machdyne/einszeit/fw/test/host/ezlib/sp80022.py

"""NIST SP 800-22 Rev 1a statistical test suite.

These tests answer "does this look random", which is a much weaker question
than "how much entropy does this carry". A well-seeded DRBG passes all fifteen
and is still useless as one-time-pad material. They are included because the
RP2350 TRNG documentation claims FIPS 140-2 conformance and because a failure
here is a strong signal that something is wrong with the capture path.

Each test returns one or more p-values. A p-value below 0.01 fails at the
conventional significance level.
"""

from __future__ import annotations

import math
from dataclasses import dataclass, field

import numpy as np
from scipy.special import erfc, gammaincc

ALPHA = 0.01


@dataclass
class TestResult:
    name: str
    p_values: list
    passed: bool
    detail: dict = field(default_factory=dict)
    skipped: str = ""

    @property
    def p_value(self) -> float:
        return self.p_values[0] if self.p_values else float("nan")


def _res(name, p, detail=None, skipped=""):
    ps = [p] if isinstance(p, float) else list(p)
    ok = all(v >= ALPHA for v in ps if v == v) if ps else False
    return TestResult(name, ps, ok, detail or {}, skipped)


def _skip(name, why):
    return TestResult(name, [], True, {}, skipped=why)


# --------------------------------------------------------------------------

def frequency(bits: np.ndarray) -> TestResult:
    n = bits.size
    s = int(bits.sum()) * 2 - n
    s_obs = abs(s) / math.sqrt(n)
    return _res("Frequency (monobit)", float(erfc(s_obs / math.sqrt(2))),
                {"sum": s, "s_obs": s_obs})


def block_frequency(bits: np.ndarray, m: int = 128) -> TestResult:
    n = bits.size
    nblocks = n // m
    if nblocks < 1:
        return _skip("Block frequency", "not enough bits")
    pi = bits[: nblocks * m].reshape(nblocks, m).mean(axis=1)
    chi2 = 4.0 * m * float(((pi - 0.5) ** 2).sum())
    return _res("Block frequency", float(gammaincc(nblocks / 2.0, chi2 / 2.0)),
                {"M": m, "N": nblocks, "chi2": chi2})


def runs(bits: np.ndarray) -> TestResult:
    n = bits.size
    pi = float(bits.mean())
    if abs(pi - 0.5) >= 2.0 / math.sqrt(n):
        return _res("Runs", 0.0, {"pi": pi, "note": "failed the monobit pre-test"})
    v = int((bits[1:] != bits[:-1]).sum()) + 1
    num = abs(v - 2.0 * n * pi * (1 - pi))
    den = 2.0 * math.sqrt(2.0 * n) * pi * (1 - pi)
    return _res("Runs", float(erfc(num / den)), {"pi": pi, "V": v})


_LONGRUN = {
    128: (8, 3, 49, [0.2148, 0.3672, 0.2305, 0.1875], 4),
    512: (16, 4, 49, [0.1174, 0.2430, 0.2493, 0.1752, 0.1027, 0.1124], 6),
    10000: (24, 6, 75, [0.0882, 0.2092, 0.2483, 0.1933, 0.1208, 0.0675, 0.0727], 10),
}


def longest_run(bits: np.ndarray) -> TestResult:
    n = bits.size
    if n >= 750_000:
        m = 10000
    elif n >= 6272:
        m = 128
    else:
        return _skip("Longest run of ones", "needs at least 6272 bits")

    _, k, n_blocks, probs, vmin = _LONGRUN[m]
    avail = n // m
    if avail < n_blocks:
        n_blocks = avail
    if n_blocks < 1:
        return _skip("Longest run of ones", "not enough blocks")

    counts = np.zeros(k + 1, dtype=np.int64)
    for i in range(n_blocks):
        block = bits[i * m : (i + 1) * m]
        longest = best = 0
        for b in block:
            best = best + 1 if b else 0
            if best > longest:
                longest = best
        idx = min(max(longest - vmin, 0), k)
        counts[idx] += 1

    exp = np.array(probs) * n_blocks
    chi2 = float((((counts - exp) ** 2) / exp).sum())
    return _res("Longest run of ones", float(gammaincc(k / 2.0, chi2 / 2.0)),
                {"M": m, "N": n_blocks, "chi2": chi2, "counts": counts.tolist()})


def binary_matrix_rank(bits: np.ndarray, m: int = 32, q: int = 32) -> TestResult:
    n = bits.size
    nmat = n // (m * q)
    if nmat < 38:
        return _skip("Binary matrix rank", "needs at least 38 matrices (38912 bits)")

    data = bits[: nmat * m * q].reshape(nmat, m, q).astype(np.uint8)
    ranks = np.array([_gf2_rank(mat) for mat in data])
    f_full = int((ranks == m).sum())
    f_one = int((ranks == m - 1).sum())
    f_rest = nmat - f_full - f_one

    probs = np.array([0.2888, 0.5776, 0.1336])
    obs = np.array([f_full, f_one, f_rest], dtype=np.float64)
    exp = probs * nmat
    chi2 = float((((obs - exp) ** 2) / exp).sum())
    return _res("Binary matrix rank", float(math.exp(-chi2 / 2.0)),
                {"matrices": nmat, "full": f_full, "full_minus_1": f_one,
                 "lower": f_rest, "chi2": chi2})


def _gf2_rank(mat: np.ndarray) -> int:
    m = mat.copy().astype(np.uint8)
    rows, cols = m.shape
    rank = 0
    for col in range(cols):
        pivot = None
        for r in range(rank, rows):
            if m[r, col]:
                pivot = r
                break
        if pivot is None:
            continue
        if pivot != rank:
            m[[rank, pivot]] = m[[pivot, rank]]
        sel = m[rank + 1 :, col] == 1
        if sel.any():
            m[rank + 1 :][sel] ^= m[rank]
        rank += 1
        if rank == rows:
            break
    return rank


def spectral_dft(bits: np.ndarray) -> TestResult:
    n = bits.size
    if n < 1000:
        return _skip("DFT (spectral)", "needs at least 1000 bits")
    x = bits.astype(np.float64) * 2.0 - 1.0
    mags = np.abs(np.fft.rfft(x)[: n // 2])
    threshold = math.sqrt(math.log(1.0 / 0.05) * n)
    n0 = 0.95 * n / 2.0
    n1 = float((mags < threshold).sum())
    d = (n1 - n0) / math.sqrt(n * 0.95 * 0.05 / 4.0)
    return _res("DFT (spectral)", float(erfc(abs(d) / math.sqrt(2))),
                {"threshold": threshold, "peaks_below": n1, "expected": n0})


_TEMPLATES_9 = [
    "000000001", "000000011", "000000101", "000001011", "000010011",
    "000100011", "000101001", "001001011", "001010011", "010101011",
]


def non_overlapping_template(bits: np.ndarray, m: int = 9,
                             nblocks: int = 8) -> TestResult:
    n = bits.size
    block_len = n // nblocks
    if block_len < m + 1:
        return _skip("Non-overlapping template", "not enough bits")

    packed = np.packbits(bits)
    del packed
    mu = (block_len - m + 1) / (2.0 ** m)
    var = block_len * (1.0 / 2.0 ** m - (2.0 * m - 1.0) / 2.0 ** (2 * m))
    if var <= 0:
        return _skip("Non-overlapping template", "variance underflow")

    p_values = []
    for tpl in _TEMPLATES_9:
        t = np.frombuffer(tpl.encode(), dtype=np.uint8) - ord("0")
        w = np.empty(nblocks)
        for j in range(nblocks):
            block = bits[j * block_len : (j + 1) * block_len]
            w[j] = _count_non_overlapping(block, t)
        chi2 = float((((w - mu) ** 2) / var).sum())
        p_values.append(float(gammaincc(nblocks / 2.0, chi2 / 2.0)))

    npass = sum(1 for p in p_values if p >= ALPHA)
    return TestResult(
        "Non-overlapping template", p_values,
        npass == len(p_values),
        {"m": m, "templates": len(_TEMPLATES_9), "passed": npass,
         "min_p": min(p_values)},
    )


def _count_non_overlapping(block: np.ndarray, tpl: np.ndarray) -> int:
    m = tpl.size
    if block.size < m:
        return 0
    view = np.lib.stride_tricks.sliding_window_view(block, m)
    hits = np.flatnonzero((view == tpl).all(axis=1))
    count = 0
    last = -m
    for h in hits:
        if h >= last + m:
            count += 1
            last = h
    return count


def overlapping_template(bits: np.ndarray, m: int = 9) -> TestResult:
    n = bits.size
    block_len = 1032
    nblocks = n // block_len
    if nblocks < 10:
        return _skip("Overlapping template", "needs at least 10320 bits")

    tpl = np.ones(m, dtype=np.uint8)
    probs = [0.364091, 0.185659, 0.139381, 0.100571, 0.070432, 0.139865]
    counts = np.zeros(6, dtype=np.int64)

    for j in range(nblocks):
        block = bits[j * block_len : (j + 1) * block_len]
        view = np.lib.stride_tricks.sliding_window_view(block, m)
        hits = int((view == tpl).all(axis=1).sum())
        counts[min(hits, 5)] += 1

    exp = np.array(probs) * nblocks
    chi2 = float((((counts - exp) ** 2) / exp).sum())
    return _res("Overlapping template", float(gammaincc(5 / 2.0, chi2 / 2.0)),
                {"N": nblocks, "chi2": chi2, "counts": counts.tolist()})


_MAURER = {
    6: (640, 5.2177052, 2.954), 7: (1280, 6.1962507, 3.125),
    8: (2560, 7.1836656, 3.238), 9: (5120, 8.1764248, 3.311),
    10: (10240, 9.1723243, 3.356), 11: (20480, 10.170032, 3.384),
    12: (40960, 11.168765, 3.401), 13: (81920, 12.168070, 3.410),
    14: (163840, 13.167693, 3.416), 15: (327680, 14.167488, 3.419),
    16: (655360, 15.167379, 3.421),
}


def maurer_universal(bits: np.ndarray) -> TestResult:
    n = bits.size
    chosen = None
    for L in range(16, 5, -1):
        q, _, _ = _MAURER[L][0], 0, 0
        if n >= (_MAURER[L][0] + 1000) * L:
            chosen = L
            break
    if chosen is None:
        return _skip("Maurer universal", "needs at least 387840 bits")

    L = chosen
    q, expected, variance = _MAURER[L]
    nblocks = n // L
    k = nblocks - q
    if k <= 0:
        return _skip("Maurer universal", "not enough blocks")

    blocks = bits[: nblocks * L].reshape(nblocks, L)
    weights = (1 << np.arange(L - 1, -1, -1)).astype(np.int64)
    vals = blocks.astype(np.int64) @ weights

    table = np.zeros(1 << L, dtype=np.int64)
    for i in range(q):
        table[vals[i]] = i + 1

    total = 0.0
    for i in range(q, nblocks):
        v = vals[i]
        total += math.log2(i + 1 - table[v]) if table[v] else math.log2(i + 1)
        table[v] = i + 1

    fn = total / k
    c = 0.7 - 0.8 / L + (4 + 32.0 / L) * (k ** (-3.0 / L)) / 15.0
    sigma = c * math.sqrt(variance / k)
    p = float(erfc(abs((fn - expected) / (math.sqrt(2) * sigma))))
    return _res("Maurer universal", p,
                {"L": L, "Q": q, "K": k, "fn": fn, "expected": expected})


def _berlekamp_massey(bits_int: int, n: int) -> int:
    """Linear complexity over GF(2), polynomials held as Python integers."""
    c, b = 1, 1
    ll, m = 0, -1
    for i in range(n):
        d = (bits_int >> (n - 1 - i)) & 1
        for j in range(1, ll + 1):
            if (c >> j) & 1:
                d ^= (bits_int >> (n - 1 - (i - j))) & 1
        if d:
            t = c
            c ^= b << (i - m)
            if 2 * ll <= i:
                ll = i + 1 - ll
                m = i
                b = t
    return ll


def linear_complexity(bits: np.ndarray, m: int = 500) -> TestResult:
    n = bits.size
    nblocks = n // m
    if nblocks < 200:
        return _skip("Linear complexity", "needs at least 100000 bits")
    nblocks = min(nblocks, 1000)  # keeps the run time sane

    mu = m / 2.0 + (9.0 + (-1) ** (m + 1)) / 36.0 - (m / 3.0 + 2.0 / 9.0) / 2.0 ** m
    probs = [0.010417, 0.03125, 0.125, 0.5, 0.25, 0.0625, 0.020833]
    counts = np.zeros(7, dtype=np.int64)

    packed = np.packbits(bits[: nblocks * m])
    for j in range(nblocks):
        block = bits[j * m : (j + 1) * m]
        as_int = int.from_bytes(np.packbits(block).tobytes(), "big") >> (
            (-m) % 8
        )
        li = _berlekamp_massey(as_int, m)
        t = ((-1) ** m) * (li - mu) + 2.0 / 9.0
        if t <= -2.5:
            idx = 0
        elif t <= -1.5:
            idx = 1
        elif t <= -0.5:
            idx = 2
        elif t <= 0.5:
            idx = 3
        elif t <= 1.5:
            idx = 4
        elif t <= 2.5:
            idx = 5
        else:
            idx = 6
        counts[idx] += 1
    del packed

    exp = np.array(probs) * nblocks
    chi2 = float((((counts - exp) ** 2) / exp).sum())
    return _res("Linear complexity", float(gammaincc(6 / 2.0, chi2 / 2.0)),
                {"M": m, "N": nblocks, "chi2": chi2, "counts": counts.tolist()})


def _psi2(bits: np.ndarray, m: int) -> float:
    if m <= 0:
        return 0.0
    n = bits.size
    ext = np.concatenate([bits, bits[: m - 1]]) if m > 1 else bits
    ids = np.zeros(n, dtype=np.int64)
    for j in range(m):
        ids = ids * 2 + ext[j : j + n]
    counts = np.bincount(ids, minlength=1 << m).astype(np.float64)
    return float((counts ** 2).sum() * (2 ** m) / n - n)


def serial(bits: np.ndarray, m: int = 16) -> TestResult:
    n = bits.size
    while m > 2 and m >= math.floor(math.log2(n)) - 2:
        m -= 1
    if m < 2:
        return _skip("Serial", "not enough bits")

    p1 = _psi2(bits, m)
    p2 = _psi2(bits, m - 1)
    p3 = _psi2(bits, m - 2)
    d1 = p1 - p2
    d2 = p1 - 2 * p2 + p3
    pa = float(gammaincc(2 ** (m - 2), d1 / 2.0))
    pb = float(gammaincc(2 ** (m - 3), d2 / 2.0))
    return _res("Serial", [pa, pb], {"m": m, "del1": d1, "del2": d2})


def approximate_entropy(bits: np.ndarray, m: int = 10) -> TestResult:
    n = bits.size
    while m > 2 and m > math.floor(math.log2(n)) - 5:
        m -= 1
    if m < 2:
        return _skip("Approximate entropy", "not enough bits")

    def phi(mm: int) -> float:
        ext = np.concatenate([bits, bits[:mm]])
        ids = np.zeros(n, dtype=np.int64)
        for j in range(mm):
            ids = ids * 2 + ext[j : j + n]
        counts = np.bincount(ids, minlength=1 << mm).astype(np.float64) / n
        nz = counts[counts > 0]
        return float((nz * np.log(nz)).sum())

    apen = phi(m) - phi(m + 1)
    chi2 = 2.0 * n * (math.log(2) - apen)
    return _res("Approximate entropy",
                float(gammaincc(2 ** (m - 1), chi2 / 2.0)),
                {"m": m, "ApEn": apen, "chi2": chi2})


def cumulative_sums(bits: np.ndarray) -> TestResult:
    n = bits.size
    x = bits.astype(np.int64) * 2 - 1
    ps = []
    for rev in (False, True):
        s = np.cumsum(x[::-1] if rev else x)
        z = int(np.abs(s).max())
        if z == 0:
            ps.append(1.0)
            continue
        total = 0.0
        from scipy.stats import norm
        k0 = int((-n / z + 1) // 4)
        k1 = int((n / z - 1) // 4)
        for k in range(k0, k1 + 1):
            total += norm.cdf((4 * k + 1) * z / math.sqrt(n))
            total -= norm.cdf((4 * k - 1) * z / math.sqrt(n))
        k0 = int((-n / z - 3) // 4)
        for k in range(k0, k1 + 1):
            total -= norm.cdf((4 * k + 3) * z / math.sqrt(n))
            total += norm.cdf((4 * k + 1) * z / math.sqrt(n))
        ps.append(max(0.0, min(1.0, 1.0 - total)))
    return _res("Cumulative sums", ps, {"forward": ps[0], "reverse": ps[1]})


_EXC_PI = {
    1: [0.5000, 0.2500, 0.1250, 0.0625, 0.0312, 0.0312],
    2: [0.7500, 0.0625, 0.0469, 0.0352, 0.0264, 0.0791],
    3: [0.8333, 0.0278, 0.0231, 0.0193, 0.0161, 0.0804],
    4: [0.8750, 0.0156, 0.0137, 0.0120, 0.0105, 0.0733],
    5: [0.9000, 0.0100, 0.0090, 0.0081, 0.0073, 0.0656],
    6: [0.9167, 0.0069, 0.0064, 0.0058, 0.0053, 0.0588],
    7: [0.9286, 0.0051, 0.0047, 0.0044, 0.0041, 0.0531],
}


def random_excursions(bits: np.ndarray) -> TestResult:
    n = bits.size
    x = bits.astype(np.int64) * 2 - 1
    s = np.concatenate(([0], np.cumsum(x), [0]))
    zero_idx = np.flatnonzero(s == 0)
    cycles = len(zero_idx) - 1
    if cycles < 500:
        return _skip("Random excursions", f"only {cycles} cycles, needs 500")

    states = [-4, -3, -2, -1, 1, 2, 3, 4]
    p_values = []
    detail = {}
    for st in states:
        counts = np.zeros(6, dtype=np.int64)
        for c in range(cycles):
            seg = s[zero_idx[c] : zero_idx[c + 1]]
            counts[min(int((seg == st).sum()), 5)] += 1
        pi = _EXC_PI[abs(st)]
        exp = np.array(pi) * cycles
        chi2 = float((((counts - exp) ** 2) / exp).sum())
        p = float(gammaincc(5 / 2.0, chi2 / 2.0))
        p_values.append(p)
        detail[str(st)] = {"chi2": chi2, "p": p}

    npass = sum(1 for p in p_values if p >= ALPHA)
    return TestResult("Random excursions", p_values, npass == len(p_values),
                      {"cycles": cycles, "passed": npass,
                       "min_p": min(p_values), "states": detail})


def random_excursions_variant(bits: np.ndarray) -> TestResult:
    n = bits.size
    x = bits.astype(np.int64) * 2 - 1
    s = np.concatenate(([0], np.cumsum(x), [0]))
    cycles = int((s == 0).sum()) - 1
    if cycles < 500:
        return _skip("Random excursions variant", f"only {cycles} cycles, needs 500")

    p_values = []
    for st in list(range(-9, 0)) + list(range(1, 10)):
        xi = int((s == st).sum())
        denom = math.sqrt(2.0 * cycles * (4.0 * abs(st) - 2.0))
        p_values.append(float(erfc(abs(xi - cycles) / denom)))

    npass = sum(1 for p in p_values if p >= ALPHA)
    return TestResult("Random excursions variant", p_values,
                      npass == len(p_values),
                      {"cycles": cycles, "passed": npass, "min_p": min(p_values)})


ALL_TESTS = [
    frequency, block_frequency, runs, longest_run, binary_matrix_rank,
    spectral_dft, non_overlapping_template, overlapping_template,
    maurer_universal, linear_complexity, serial, approximate_entropy,
    cumulative_sums, random_excursions, random_excursions_variant,
]


def run_all(bits: np.ndarray, skip_slow: bool = False) -> list:
    slow = {linear_complexity, non_overlapping_template, random_excursions}
    out = []
    for fn in ALL_TESTS:
        if skip_slow and fn in slow:
            out.append(_skip(fn.__name__.replace("_", " ").title(), "skipped (fast mode)"))
            continue
        try:
            out.append(fn(bits))
        except Exception as exc:  # a failed test must not lose the whole report
            out.append(TestResult(fn.__name__, [], False, {"error": str(exc)}))
    return out


def summarise(results: list) -> dict:
    ran = [r for r in results if not r.skipped and r.p_values]
    failed = [r.name for r in ran if not r.passed]
    return {
        "total": len(results),
        "ran": len(ran),
        "skipped": len(results) - len(ran),
        "failed": failed,
        "pass": len(failed) == 0,
    }


# ---------------------------------------------------------------------------
# Multi-sequence assessment
# ---------------------------------------------------------------------------
#
# SP 800-22 is not designed around a single p-value from one long sequence. The
# suite partitions the data into m sequences, runs every test on each, and
# applies two acceptance criteria: the proportion of sequences passing must
# fall inside a confidence interval, and the p-values must be uniformly
# distributed over (0,1).
#
# This also resolves the random excursion problem. Those two tests apply only
# to sequences whose +-1 walk returns to zero at least 500 times, and whether
# any single sequence qualifies is close to a coin toss: the number of returns
# behaves like sqrt(n)*|N(0,1)|, so even at 10^8 bits a sequence fails to
# qualify about 4% of the time. Across m sequences enough of them qualify, and
# the suite scores only those, which is exactly what NIST intends.

def proportion_bounds(m: int, alpha: float = ALPHA) -> tuple:
    """NIST acceptance interval for the proportion of passing sequences."""
    p_hat = 1.0 - alpha
    margin = 3.0 * math.sqrt(p_hat * alpha / m)
    return (max(0.0, p_hat - margin), min(1.0, p_hat + margin))


def pvalue_uniformity(p_values: list) -> float:
    """Chi-square over 10 equal bins; NIST rejects below 0.0001."""
    if len(p_values) < 10:
        return float("nan")
    counts = np.histogram(np.asarray(p_values), bins=10, range=(0.0, 1.0))[0]
    expected = len(p_values) / 10.0
    chi2 = float((((counts - expected) ** 2) / expected).sum())
    return float(gammaincc(9 / 2.0, chi2 / 2.0))


def run_multi(bits: np.ndarray, nseq: int = 0, seq_bits: int = 1_000_000,
              skip_slow: bool = False) -> dict:
    """Partition into sequences, run the suite on each, and score the set."""
    if nseq <= 0:
        nseq = max(1, bits.size // seq_bits)
    seq_bits = bits.size // nseq
    if seq_bits < 100_000:
        return {"error": f"sequences of {seq_bits:,} bits are too short; "
                         f"supply more data or fewer sequences"}

    # Several tests emit more than one p-value per sequence: 10 templates for
    # non-overlapping template, 8 states for random excursions, 18 for its
    # variant, 2 each for serial and cumulative sums. NIST scores each of those
    # sub-tests separately, with its own proportion across sequences.
    #
    # Collapsing them into one pass/fail per sequence, as this did originally,
    # multiplies the expected failure rate by the number of sub-tests while
    # leaving the acceptance bound calibrated for a single one. Non-overlapping
    # template then has an expected pass rate of 0.99^10 = 0.904 and gets
    # measured against a bound of 0.960, so a healthy source fails by
    # construction.
    per_test: dict = {}
    for i in range(nseq):
        seq = bits[i * seq_bits : (i + 1) * seq_bits]
        for r in run_all(seq, skip_slow=skip_slow):
            rec = per_test.setdefault(r.name, {"skipped": 0, "by_index": {}})
            if r.skipped:
                rec["skipped"] += 1
                continue
            for j, v in enumerate(r.p_values):
                if v == v:
                    rec["by_index"].setdefault(j, []).append(v)

    lo, hi = proportion_bounds(nseq)
    results = []
    for name, rec in per_test.items():
        by_index = rec["by_index"]
        if not by_index:
            results.append({"test": name, "ran": 0, "skipped": rec["skipped"],
                            "verdict": "not applicable to any sequence"})
            continue

        subs, all_p = [], []
        for j in sorted(by_index):
            pv = by_index[j]
            n = len(pv)
            passes = sum(1 for v in pv if v >= ALPHA)
            blo, _ = proportion_bounds(n)
            subs.append({"index": j, "ran": n, "passed": passes,
                         "proportion": passes / n, "bound": blo,
                         "ok": passes / n >= blo,
                         # A shortfall smaller than one sequence is the integer
                         # coarseness of the bound, not evidence of anything.
                         "marginal": (passes / n < blo
                                      and (passes + 1) / n >= blo)})
            all_p.extend(pv)

        worst = min(subs, key=lambda x: x["proportion"])
        unif = pvalue_uniformity(all_p)
        failing = [x for x in subs if not x["ok"] and not x["marginal"]]
        marginal = [x for x in subs if x["marginal"]]
        ok = not failing and (unif != unif or unif >= 0.0001)

        results.append({
            "test": name, "subtests": len(subs),
            "ran": worst["ran"], "skipped": rec["skipped"],
            "passed": worst["passed"], "proportion": worst["proportion"],
            "bounds": [worst["bound"], 1.0], "uniformity_p": unif,
            "p_values": all_p[:6],
            "min_p": min(all_p) if all_p else float("nan"),
            "median_p": float(np.median(all_p)) if all_p else float("nan"),
            "n_failing_subtests": len(failing),
            "n_marginal_subtests": len(marginal),
            "verdict": ("pass" if ok else "fail") if not marginal or failing
                       else "marginal",
        })

    failed = [r["test"] for r in results if r.get("verdict") == "fail"]

    # With few sequences the proportion criterion is coarse and the p-value
    # uniformity criterion needs at least ten sequences to mean anything, so a
    # "pass" here is weak evidence. Flag tests whose p-values all sit low: that
    # is a consistent effect the pass/fail split hides.
    marginal = [r["test"] for r in results if r.get("verdict") == "marginal"]

    return {
        "marginal": marginal,
        "weak_criterion": nseq < 10,
        "sequences": nseq,
        "bits_per_sequence": seq_bits,
        "proportion_bounds": [lo, hi],
        "tests": sorted(results, key=lambda r: r["test"]),
        "failed": failed,
        "pass": not failed,
    }
